eutectic6337/TNbadge/dc615-guitar-skyline.png

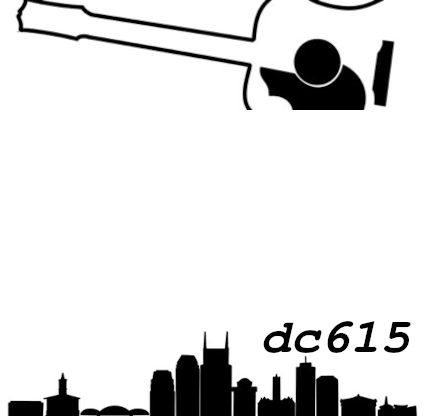
dc615-guitar-skyline.png
