eutectic6337/TNbadge/hardware/3Dback.png

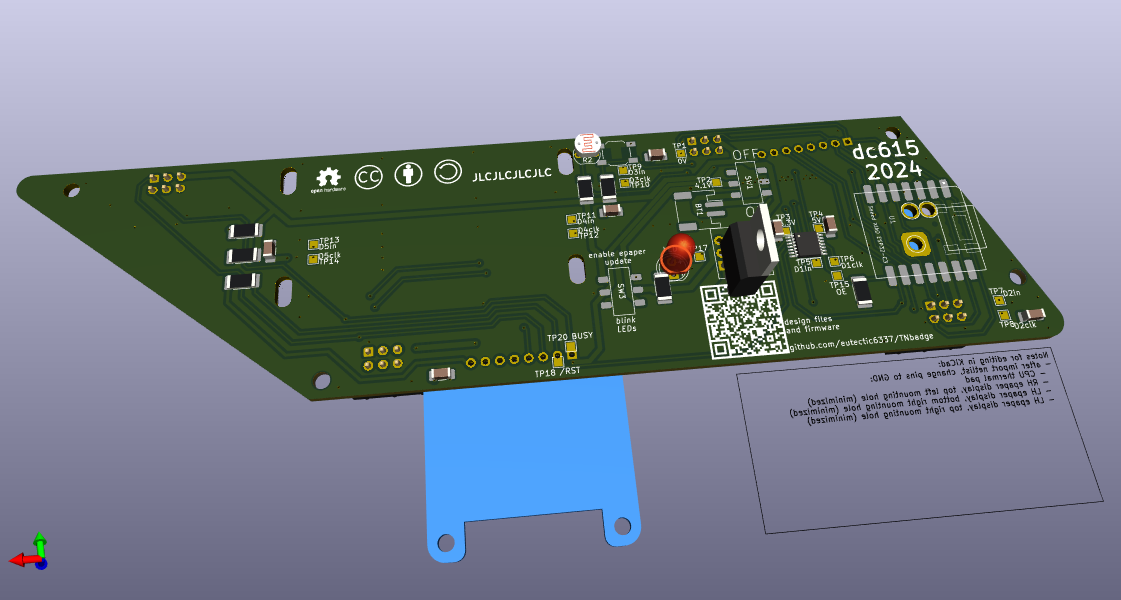
hardware/3Dback.png
