eutectic6337/TNbadge/hardware/3Dfront.png

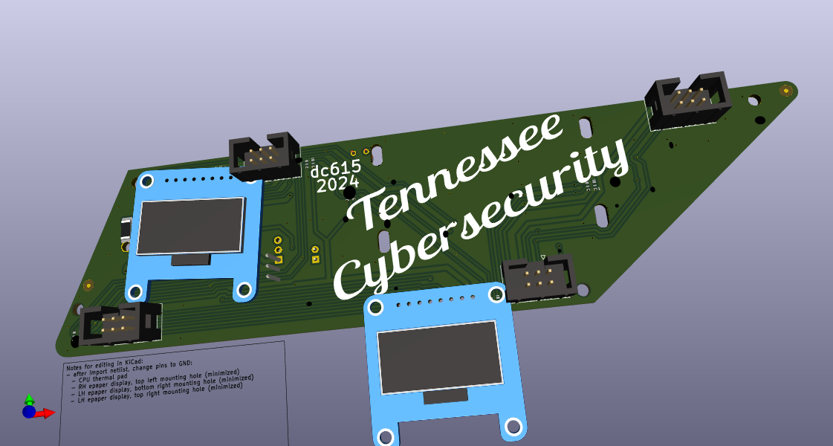
hardware/3Dfront.png
