eutectic6337/TNbadge/hardware/i/03-APA102-a.jpg

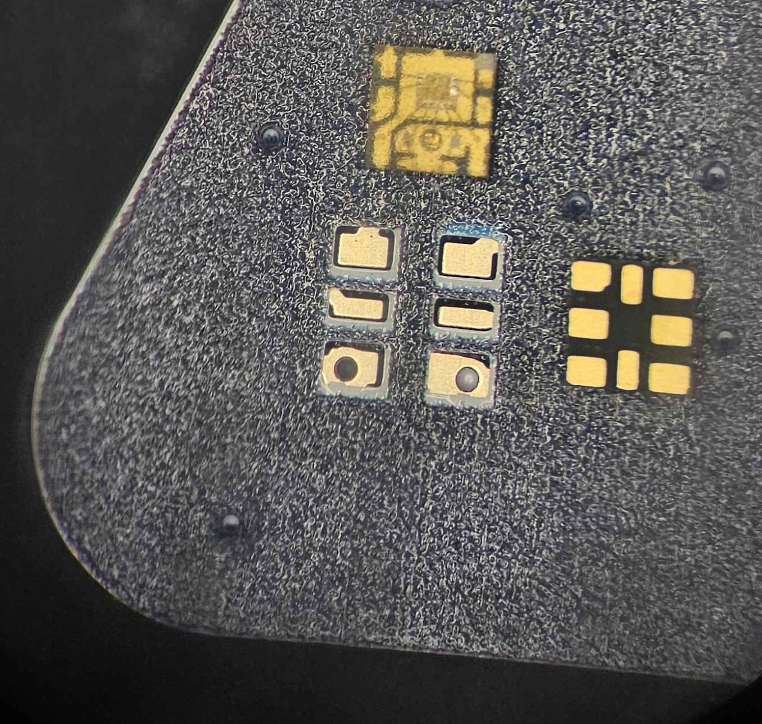
hardware/i/03-APA102-a.jpg
