eutectic6337/TNbadge/hardware/i/05-pbsw-a.jpg

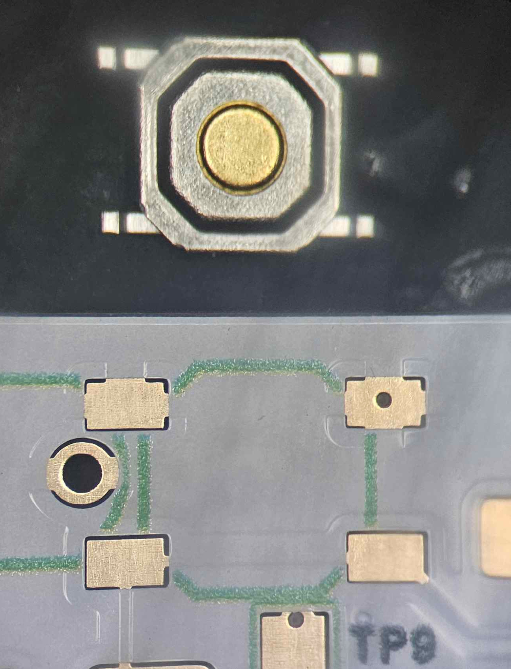
hardware/i/05-pbsw-a.jpg
