eutectic6337/TNbadge/hardware/i/07-10k-a.jpg

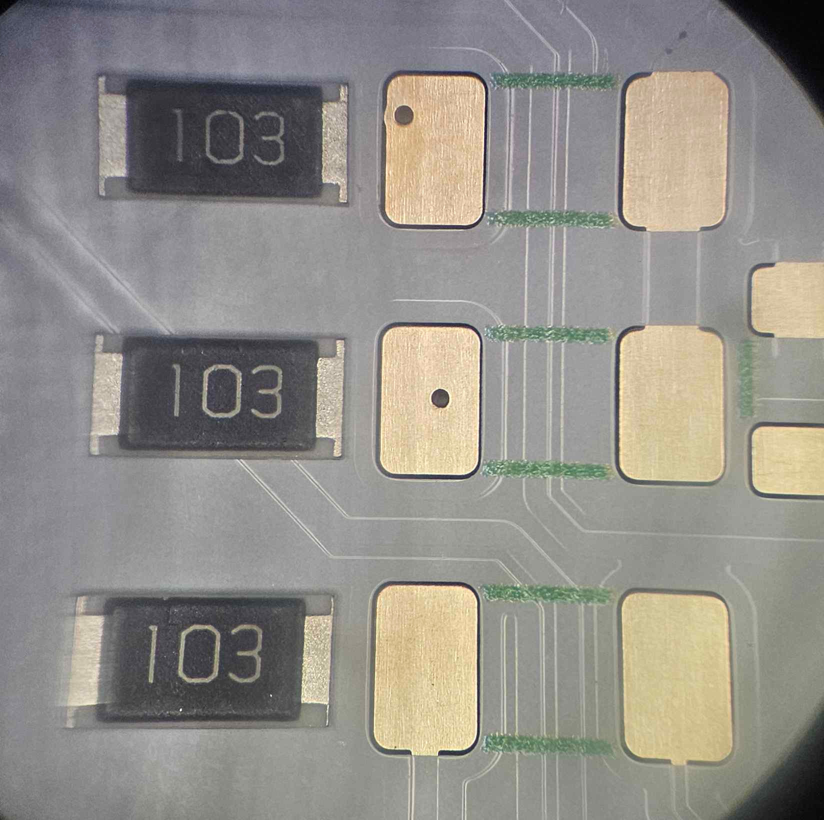
hardware/i/07-10k-a.jpg
