eutectic6337/TNbadge/hardware/i/07-10k-b.jpg

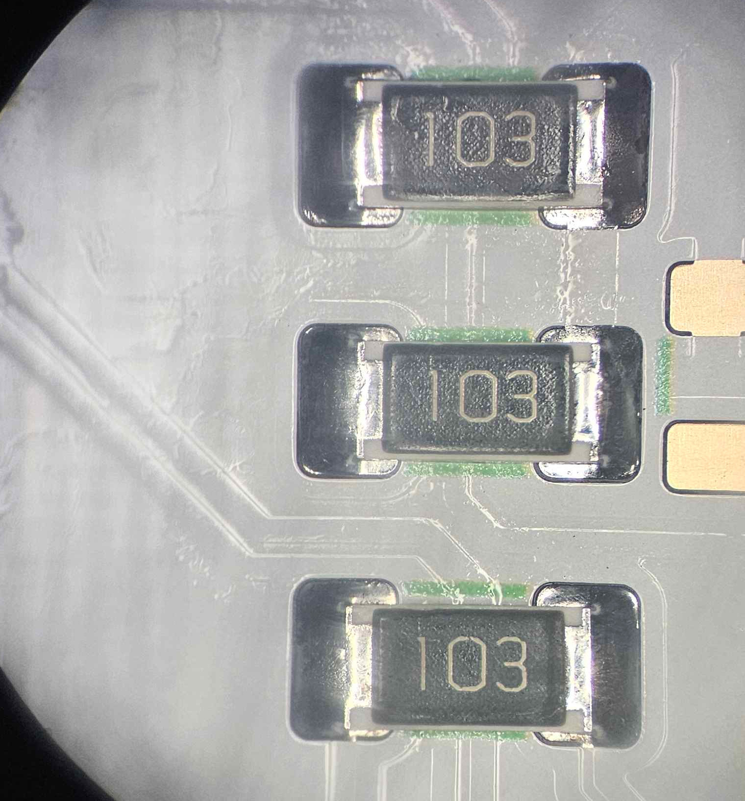
hardware/i/07-10k-b.jpg
