eutectic6337/TNbadge/hardware/i/08-1uF-a.jpg

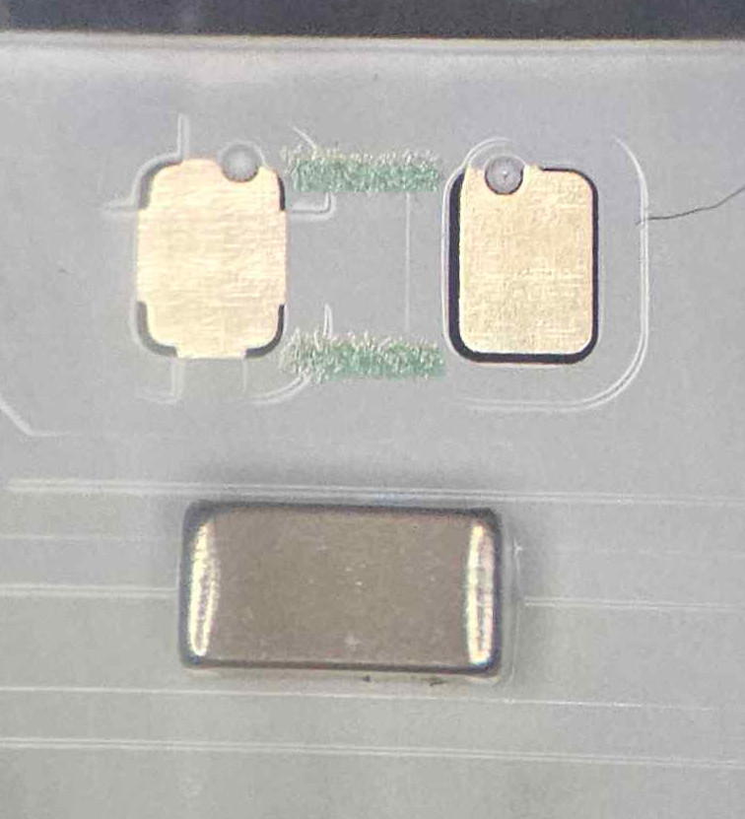
hardware/i/08-1uF-a.jpg
