eutectic6337/TNbadge/hardware/i/08-1uF-b.jpg

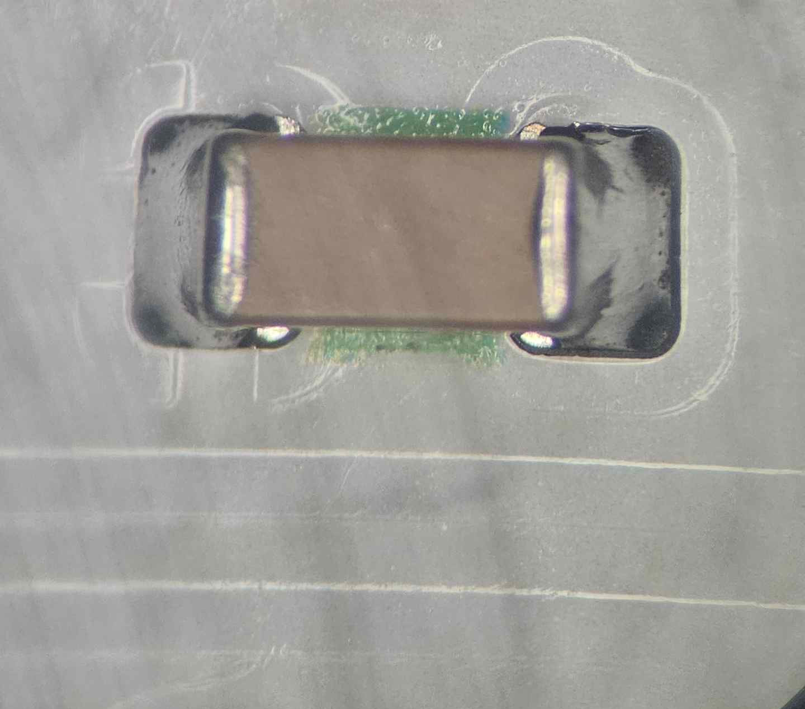
hardware/i/08-1uF-b.jpg
