eutectic6337/TNbadge/hardware/i/09-pow_sw-a.jpg

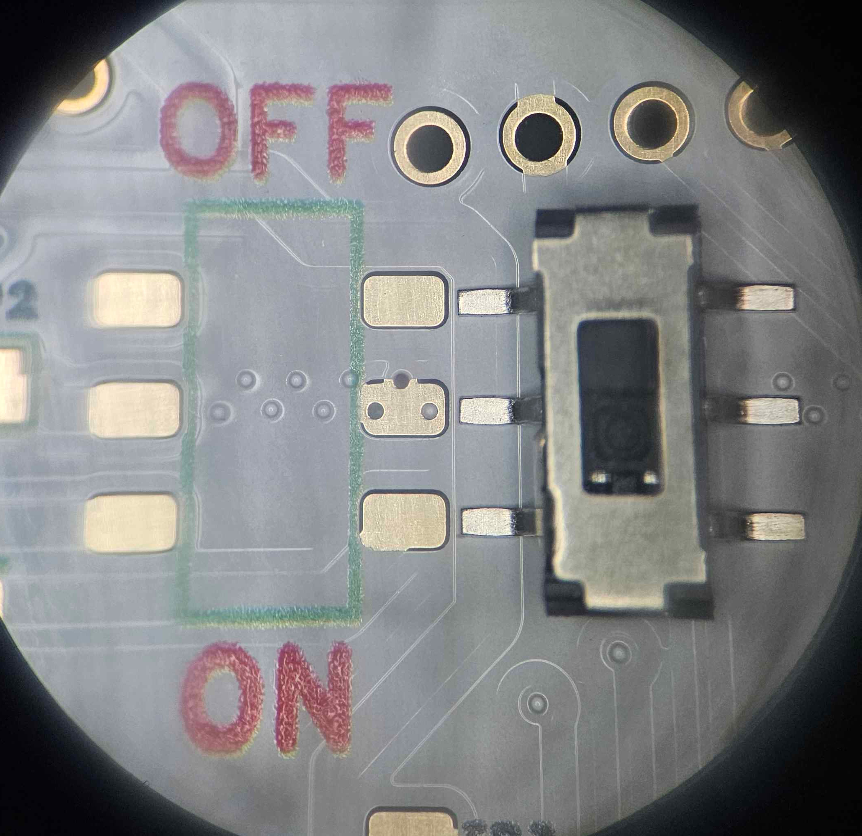
hardware/i/09-pow_sw-a.jpg
