eutectic6337/TNbadge/hardware/i/09-pow_sw-b.jpg

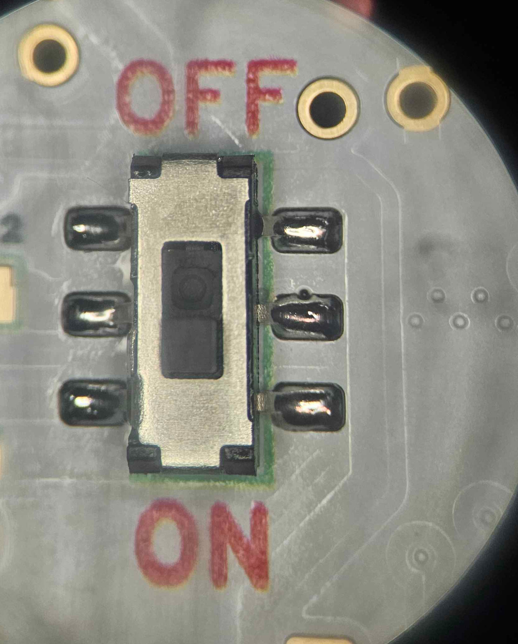
hardware/i/09-pow_sw-b.jpg
