eutectic6337/TNbadge/hardware/i/11-batcon-a.jpg

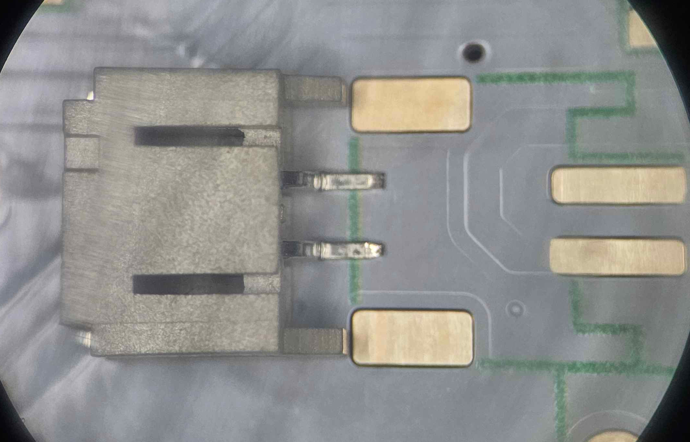
hardware/i/11-batcon-a.jpg
