eutectic6337/TNbadge/hardware/i/11-batcon-b.jpg

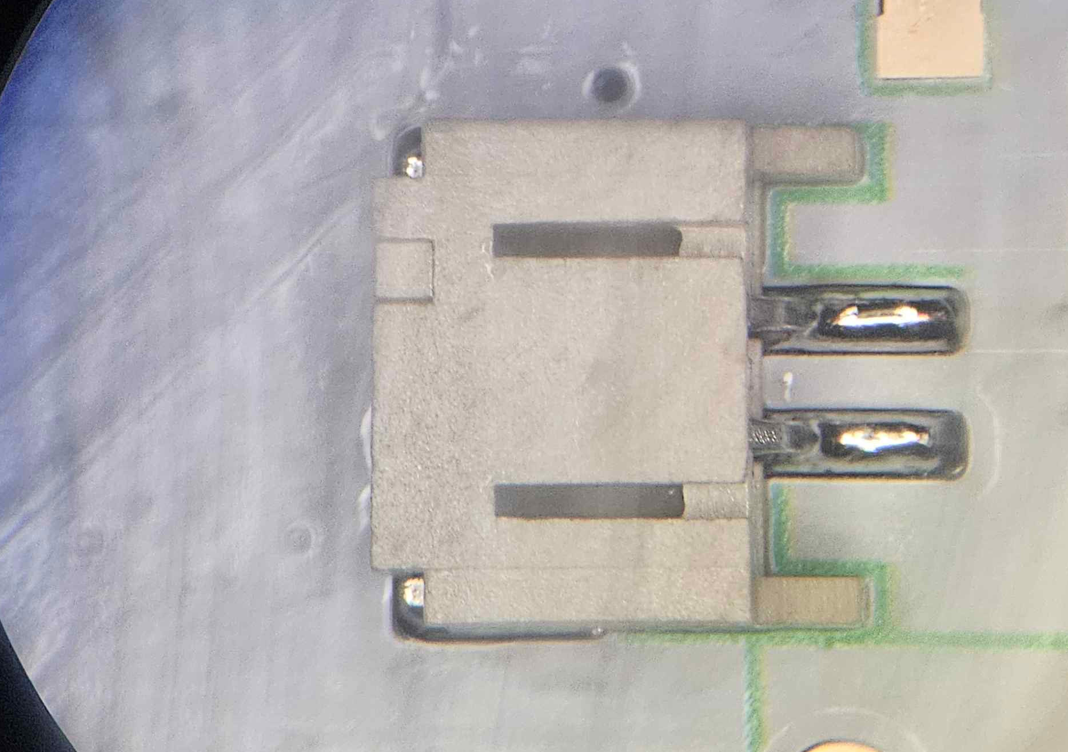
hardware/i/11-batcon-b.jpg
