eutectic6337/TNbadge/hardware/i/bare_PCB-both_sides.jpg

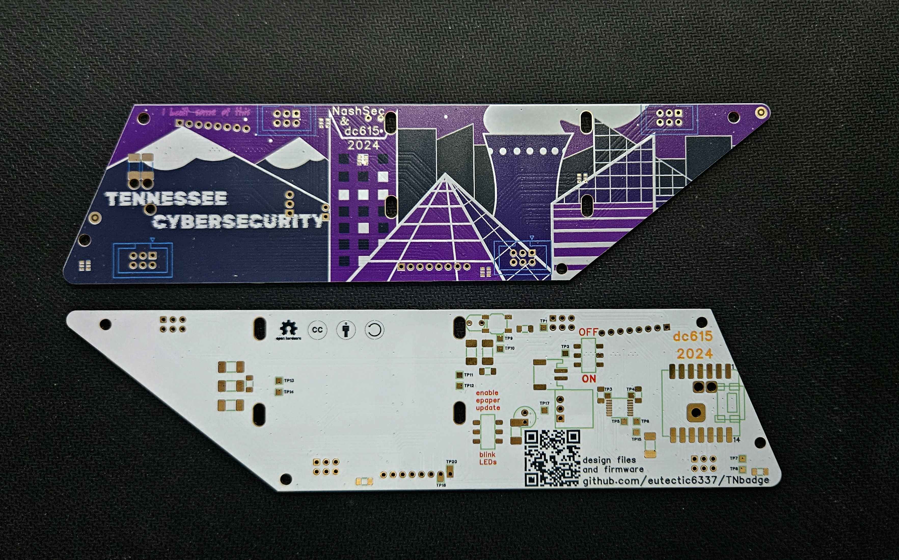
hardware/i/bare_PCB-both_sides.jpg
