eutectic6337/TNbadge/hardware/SVG/TEXT_CYBERSECURITY.png

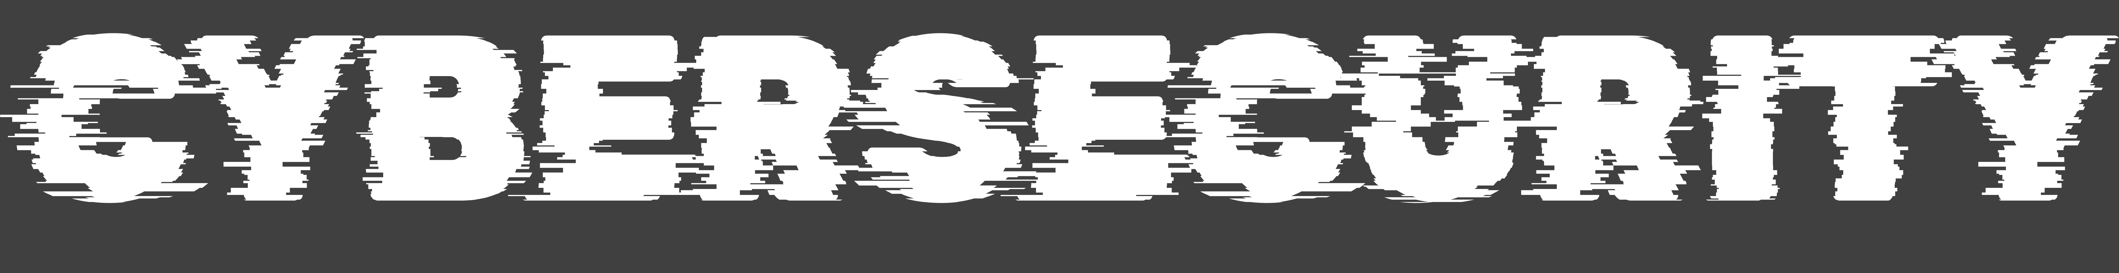
hardware/SVG/TEXT_CYBERSECURITY.png
