eutectic6337/TNbadge/hardware/SVG/TEXT_TENNESSEE.png

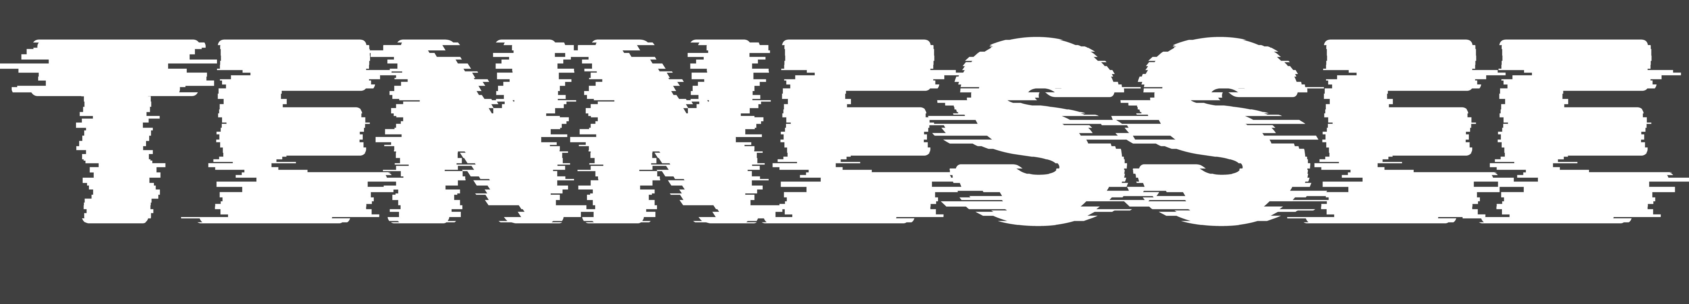
hardware/SVG/TEXT_TENNESSEE.png
