eutectic6337/TNbadge/hardware/badge.kicad_sch

## KiCad design hardware/badge.kicad_sch (2024-04-19)

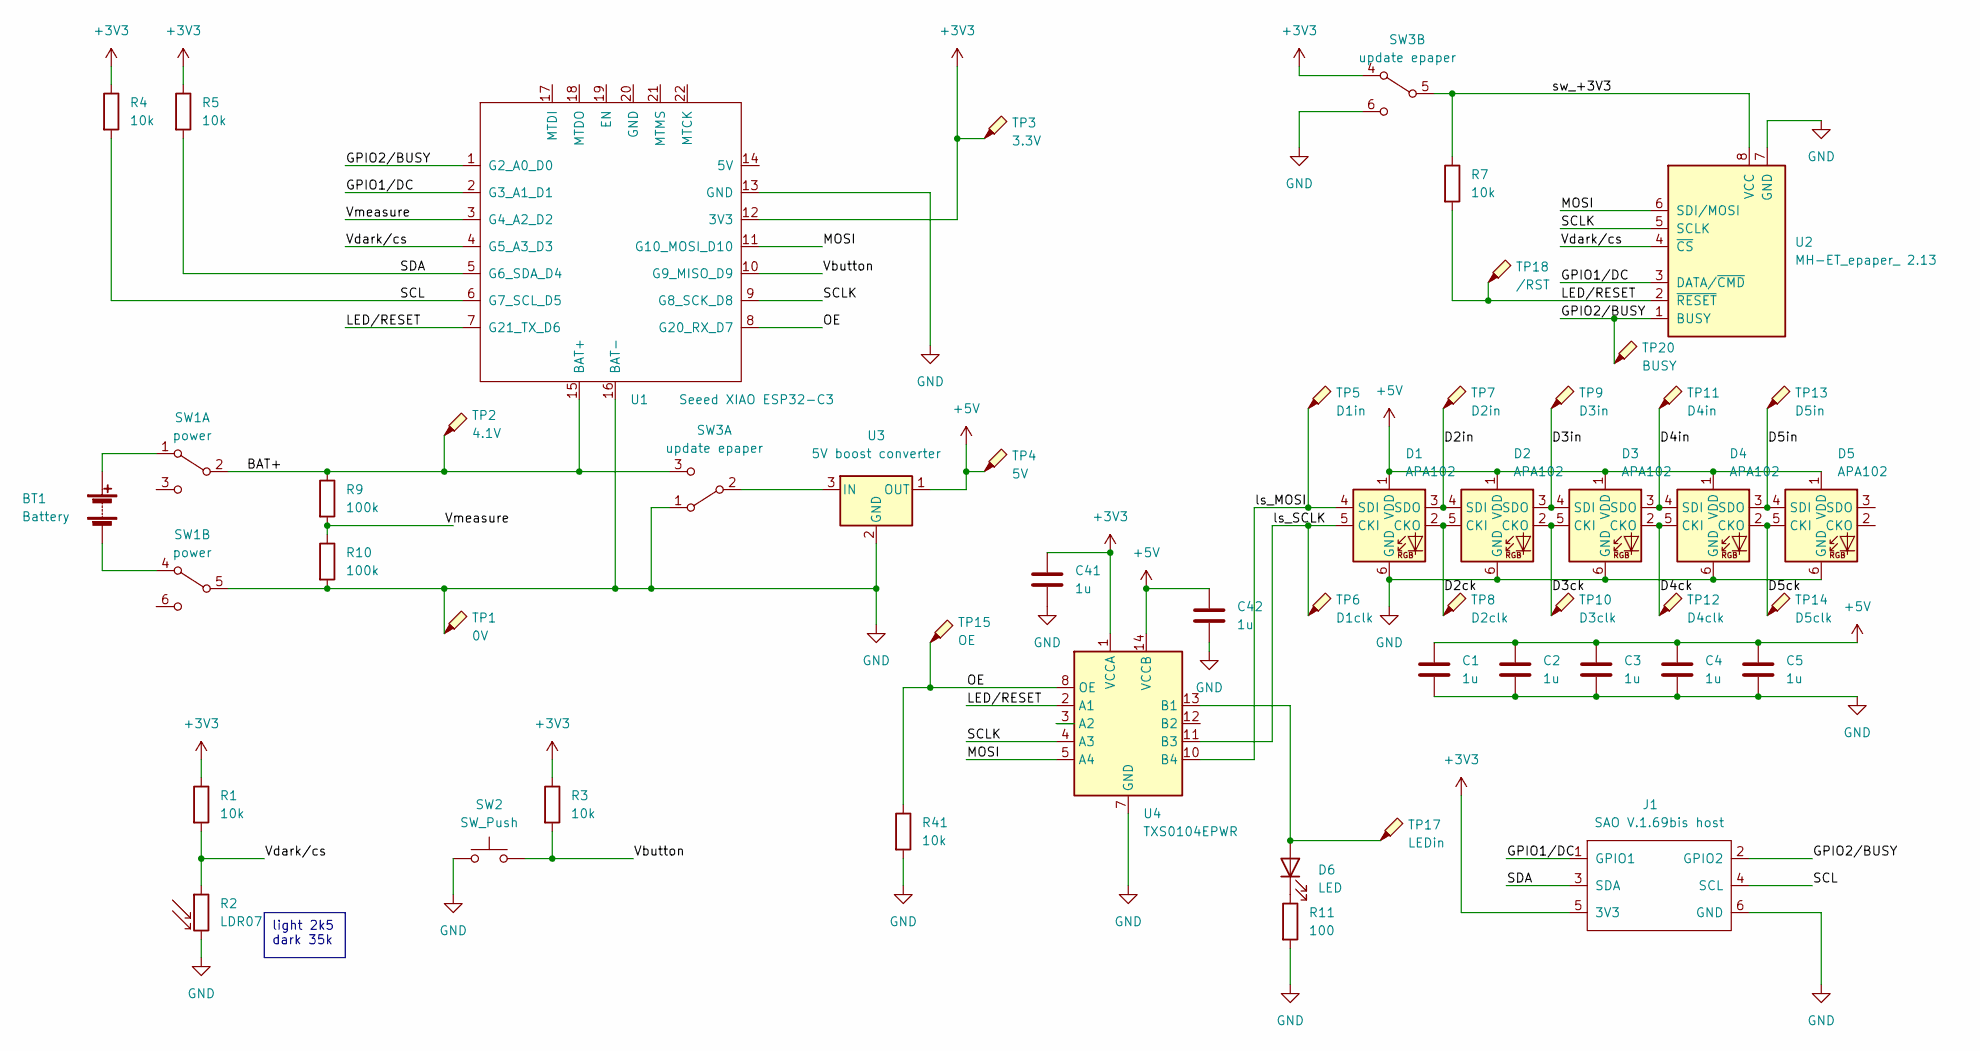
[picture p47: schematic badge.kicad_sch]

Parts:
BT1: Battery; JST_PH_S2B-PH-SM4-TB_1x02-1MP_P2.00mm_Horizontal
C1, C2, C3, C4, C5, C41, C42: 1u; C_1206_3216Metric_Pad1.33x1.80mm_HandSolder
D1, D2, D3, D4, D5: APA102; LED-APA102-2020
D6: LED; LED_D5.0mm
J1: SAO V.1.69bis host; IDC-Header_2x03_P2.54mm_Vertical
R1, R3, R4, R5, R7, R41: 10k; R_2010_5025Metric_Pad1.40x2.65mm_HandSolder
R2: LDR07; R_LDR_5.1x4.3mm_P3.4mm_Vertical
R9, R10: 100k; R_2010_5025Metric_Pad1.40x2.65mm_HandSolder
R11: 100; R_2010_5025Metric_Pad1.40x2.65mm_HandSolder
SW1: power; MSS-22D18G2 hand-solderable
SW2: SW_Push; SW_SPST_SKQG_WithoutStem
SW3: update epaper; MSS-22D18G2 hand-solderable
TP1: 0V; TestPoint_Pad_1.5x1.5mm
TP2: 4.1V; TestPoint_Pad_1.5x1.5mm
TP3: 3.3V; TestPoint_Pad_1.5x1.5mm
TP4: 5V; TestPoint_Pad_1.5x1.5mm
TP5: D1in; TestPoint_Pad_1.5x1.5mm
TP6: D1clk; TestPoint_Pad_1.5x1.5mm
TP7: D2in; TestPoint_Pad_1.5x1.5mm
TP8: D2clk; TestPoint_Pad_1.5x1.5mm
TP9: D3in; TestPoint_Pad_1.5x1.5mm
TP10: D3clk; TestPoint_Pad_1.5x1.5mm
TP11: D4in; TestPoint_Pad_1.5x1.5mm
TP12: D4clk; TestPoint_Pad_1.5x1.5mm
TP13: D5in; TestPoint_Pad_1.5x1.5mm
TP14: D5clk; TestPoint_Pad_1.5x1.5mm
TP15: OE; TestPoint_Pad_1.5x1.5mm
TP17: LEDin; TestPoint_Pad_1.5x1.5mm
TP18: /RST; TestPoint_Pad_1.5x1.5mm
TP20: BUSY; TestPoint_Pad_1.5x1.5mm
U1: Seeed XIAO ESP32-C3; Seeed XIAO ESP32-C3 hand-solderable
U2: MH-ET_epaper_ 2.13
U3: 5V boost converter; boost converter module
U4: TXS0104EPWR; TSSOP-14_4.4x5mm_P0.65mm

Connections:
+3V3: C41.1, J1.5 (3V3), R1.1, R3.1, R4.1, R5.1, SW3.4 (A), TP3.1, U1.12 (3V3), U4.1 (VCCA)
+5V: C1.1, C2.1, C3.1, C4.1, C5.1, C42.1, D1.1 (VDD), D2.1 (VDD), D3.1 (VDD), D4.1 (VDD), D5.1 (VDD), TP4.1, U3.1 (OUT), U4.14 (VCCB)
BAT+: R9.1, SW1.2 (B), SW3.3 (C), TP2.1, U1.15 (BAT+)
D2ck: D1.2 (CKO), D2.5 (CKI), TP8.1
D2in: D1.3 (SDO), D2.4 (SDI), TP7.1
D3ck: D2.2 (CKO), D3.5 (CKI), TP10.1
D3in: D2.3 (SDO), D3.4 (SDI), TP9.1
D4ck: D3.2 (CKO), D4.5 (CKI), TP12.1
D4in: D3.3 (SDO), D4.4 (SDI), TP11.1
D5ck: D4.2 (CKO), D5.5 (CKI), TP14.1
D5in: D4.3 (SDO), D5.4 (SDI), TP13.1
GND: C1.2, C2.2, C3.2, C4.2, C5.2, C41.2, C42.2, D1.6 (GND), D2.6 (GND), D3.6 (GND), D4.6 (GND), D5.6 (GND), J1.6 (GND), R2.2, R10.2, R11.2, R41.2, SW1.5 (B), SW2.1, SW3.1 (A), SW3.6 (C), TP1.1, U1.13 (GND), U1.16 (BAT-), U2.7 (GND), U3.2 (GND), U4.7 (GND)
GPIO1/DC: J1.1 (GPIO1), U1.2 (G3_A1_D1), U2.3 (DATA/~CMD)
GPIO2/BUSY: J1.2 (GPIO2), TP20.1, U1.1 (G2_A0_D0), U2.1 (BUSY)
LED/RESET: R7.2, TP18.1, U1.7 (G21_TX_D6), U2.2 (~RESET), U4.2 (A1)
MOSI: U1.11 (G10_MOSI_D10), U2.6 (SDI/MOSI), U4.5 (A4)
unnamed: BT1.1 (-), SW1.4 (A)
unnamed: BT1.2 (+), SW1.1 (A)
unnamed: D6.1 (K), R11.1
unnamed: D6.2 (A), TP17.1, U4.13 (B1)
unnamed: SW3.2 (B), U3.3 (IN)
OE: R41.1, TP15.1, U1.8 (G20_RX_D7), U4.8 (OE)
SCL: J1.4 (SCL), R4.2, U1.6 (G7_SCL_D5)
SCLK: U1.9 (G8_SCK_D8), U2.5 (SCLK), U4.4 (A3)
SDA: J1.3 (SDA), R5.2, U1.5 (G6_SDA_D4)
Vbutton: R3.2, SW2.2, U1.10 (G9_MISO_D9)
Vdark/cs: R1.2, R2.1, U1.4 (G5_A3_D3), U2.4 (~CS)
Vmeasure: R9.2, R10.1, U1.3 (G4_A2_D2)
ls_MOSI: D1.4 (SDI), TP5.1, U4.10 (B4)
ls_SCLK: D1.5 (CKI), TP6.1, U4.11 (B3)
sw_+3V3: R7.1, SW3.5 (B), U2.8 (VCC)

Notes on the sheet:
light 2k5 dark 35k
