eutectic6337/TNbadge/software/module-tests/5-Cylon-smartLEDs/5-Cylon-smartLEDs.ino

/*
  validate TNbadge hardware, one module at a time

  based on
  Examples/FastLED/Cylon

  Move a single LED back and forth (Larson Scanner effect)
*/

#include <FastLED.h>

// How many leds in your strip?
#define NUM_LEDS 5

// For led chipsets that are SPI based (four wires - data, clock,
// ground, and power), like the LPD8806 define both DATA_PIN and CLOCK_PIN
// Clock pin only needed for SPI based chipsets when not using hardware SPI
#define DATA_PIN MOSI
#define CLOCK_PIN SCK

// Define the array of leds
CRGB leds[NUM_LEDS];

void setup() { 
	Serial.begin(57600);
	Serial.println("resetting");
  FastLED.addLeds<APA102, DATA_PIN, CLOCK_PIN, RGB>(leds, NUM_LEDS);  // BGR ordering is typical
	FastLED.setBrightness(84);
}

void fadeall() { for(int i = 0; i < NUM_LEDS; i++) { leds[i].nscale8(250); } }

void loop() { 
	static uint8_t hue = 0;
	Serial.print("x");
	// First slide the led in one direction
	for(int i = 0; i < NUM_LEDS; i++) {
		// Set the i'th led to red 
		leds[i] = CHSV(hue++, 255, 255);
		// Show the leds
		FastLED.show(); 
		// now that we've shown the leds, reset the i'th led to black
		// leds[i] = CRGB::Black;
		fadeall();
		// Wait a little bit before we loop around and do it again
		delay(10);
	}
	Serial.print("x");

	// Now go in the other direction.  
	for(int i = (NUM_LEDS)-1; i >= 0; i--) {
		// Set the i'th led to red 
		leds[i] = CHSV(hue++, 255, 255);
		// Show the leds
		FastLED.show();
		// now that we've shown the leds, reset the i'th led to black
		// leds[i] = CRGB::Black;
		fadeall();
		// Wait a little bit before we loop around and do it again
		delay(10);
	}
}
